mladendinic/nixietap/hardware/photos/DSC08158.JPG

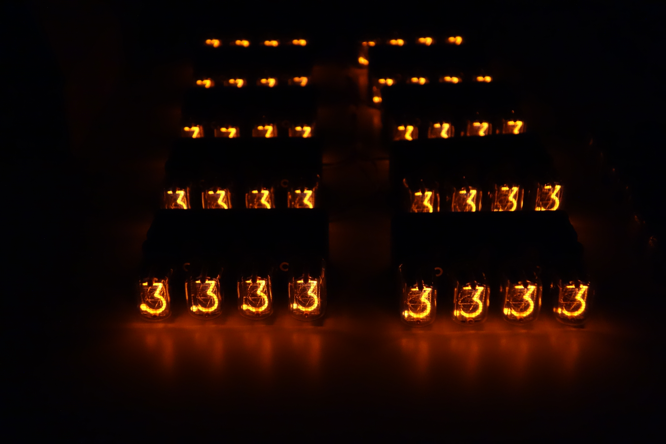
hardware/photos/DSC08158.JPG
